Timo614/Xiao-MG24-Showdown-Dog-Beep-Reinforcer/src/mazel.h

#ifndef MAZEL_H
#define MAZEL_H

#include <stdint.h>
#if defined(__AVR__)
  #include <avr/pgmspace.h>
#endif

// Generated from Flipper Zero SubGhz RAW capture
// Frequency: 433889000 Hz (~433.889 MHz)
// Protocol: RAW
// Total timing values: 4226

static const int32_t Mazel[] PROGMEM = {
    165, -2490, 133, -66, 199, -564, 197, -66, 67, -230, 563, -264, 165, -298, 131, -66, 229, -132, 131, -230, 2831, -66, 1249, -756,
    2977, -7600, 393, -396, 133, -100, 165, -266, 231, -2408, 361, -196, 231, -528, 295, -132, 197, -498, 267, -166, 131, -166, 65, -17874,
    131, -1328, 131, -2920, 397, -200, 333, -332, 299, -66, 231, -928, 229, -166, 295, -164, 163, -788, 295, -100, 195, -1188, 331, -134,
    2227, -66, 861, -5752, 65, -98, 97, -98, 165, -1162, 7777, -15348, 63, -168, 233, -166, 329, -98, 199, -636, 65, -66, 297, -100,
    297, -164, 231, -460, 231, -132, 427, -98, 923, -100, 523, -100, 625, -132, 2249, -4124, 199, -2356, 297, -132, 99, -2616, 131, -230,
    131, -198, 65, -298, 1061, -1578, 363, -130, 229, -166, 63, -66, 197, -196, 261, -954, 233, -330, 97, -100, 525, -332, 263, -164,
    97, -66, 263, -10812, 229, -130, 2731, -100, 131, -17336, 431, -200, 729, -298, 331, -98, 199, -98, 529, -298, 331, -200, 163, -268,
    265, -132, 497, -1162, 395, -2308, 365, -98, 401, -98, 231, -100, 267, -100, 2209, -7012, 3051, -166, 267, -198, 99, -100, 263, -166,
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
    227, -758, 741, -276, 217, -752, 239, -766, 227, -760, 255, -758, 225, -758, 237, -776, 247, -752, 227, -766, 223, -6452, 1509, -1042,
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
};

static constexpr size_t MazelCount = sizeof(Mazel) / sizeof(Mazel[0]);

#endif // MAZEL_H
