Timo614/Xiao-MG24-Showdown-Dog-Beep-Reinforcer/src/mensch.h

#ifndef MENSCH_H
#define MENSCH_H

#include <stdint.h>
#if defined(__AVR__)
  #include <avr/pgmspace.h>
#endif
// Generated from Flipper Zero SubGhz RAW capture
// Frequency: 433889000 Hz (~433.889 MHz)
// Protocol: RAW
// Total timing values: 4237

static const int32_t Mensch[] PROGMEM = {
    5103, -756, 1403, -6692, 65, -862, 963, -98, 399, -132, 299, -1230, 65, -132, 99, -794, 363, -132, 359, -132, 459, -132, 329, -134,
    195, -132, 295, -164, 229, -164, 263, -164, 65, -98, 195, -132, 229, -562, 65, -100, 231, -264, 65, -100, 295, -164, 65, -66,
    229, -660, 893, -68, 4229, -7614, 199, -566, 429, -66, 429, -232, 327, -164, 265, -198, 295, -66, 325, -166, 331, -66, 263, -102,
    299, -100, 497, -630, 757, -98, 427, -132, 233, -166, 233, -134, 265, -398, 97, -66, 263, -98, 425, -98, 1419, -66, 6949, -496,
    131, -264, 163, -330, 131, -6352, 99, -100, 295, -132, 233, -134, 499, -66, 265, -100, 265, -68, 365, -66, 495, -66, 2587, -9364,
    65, -166, 99, -1290, 297, -166, 297, -132, 493, -98, 263, -66, 395, -100, 729, -100, 525, -66, 361, -130, 231, -100, 401, -132,
    333, -66, 331, -332, 199, -100, 1725, -134, 333, -98, 2017, -6028, 65, -2542, 65, -296, 165, -132, 65, -164, 327, -66, 297, -164,
    6739, -102, 365, -98, 297, -66, 729, -98, 299, -132, 1293, -66, 4571, -430, 65, -1614, 65, -3724, 129, -100, 63, -198, 195, -132,
    131, -100, 97, -498, 65, -230, 65, -164, 659, -2050, 425, -66, 365, -66, 229, -366, 295, -296, 329, -98, 489, -132, 131, -164,
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
    227, -798, 203, -766, 221, -796, 215, -766, 245, -756, 227, -772, 711, -274, 733, -282, 717, -260, 717, -290, 733, -276, 217, -764,
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
};

static constexpr size_t MenschCount = sizeof(Mensch) / sizeof(Mensch[0]);

#endif // MENSCH_H
